Krasrepen/DISTRIBUTORE-AUTOMATICO/schema elettrico/SchemaElettrico.kicad_sch

## KiCad design schema elettrico/SchemaElettrico.kicad_sch (2025-07-13)

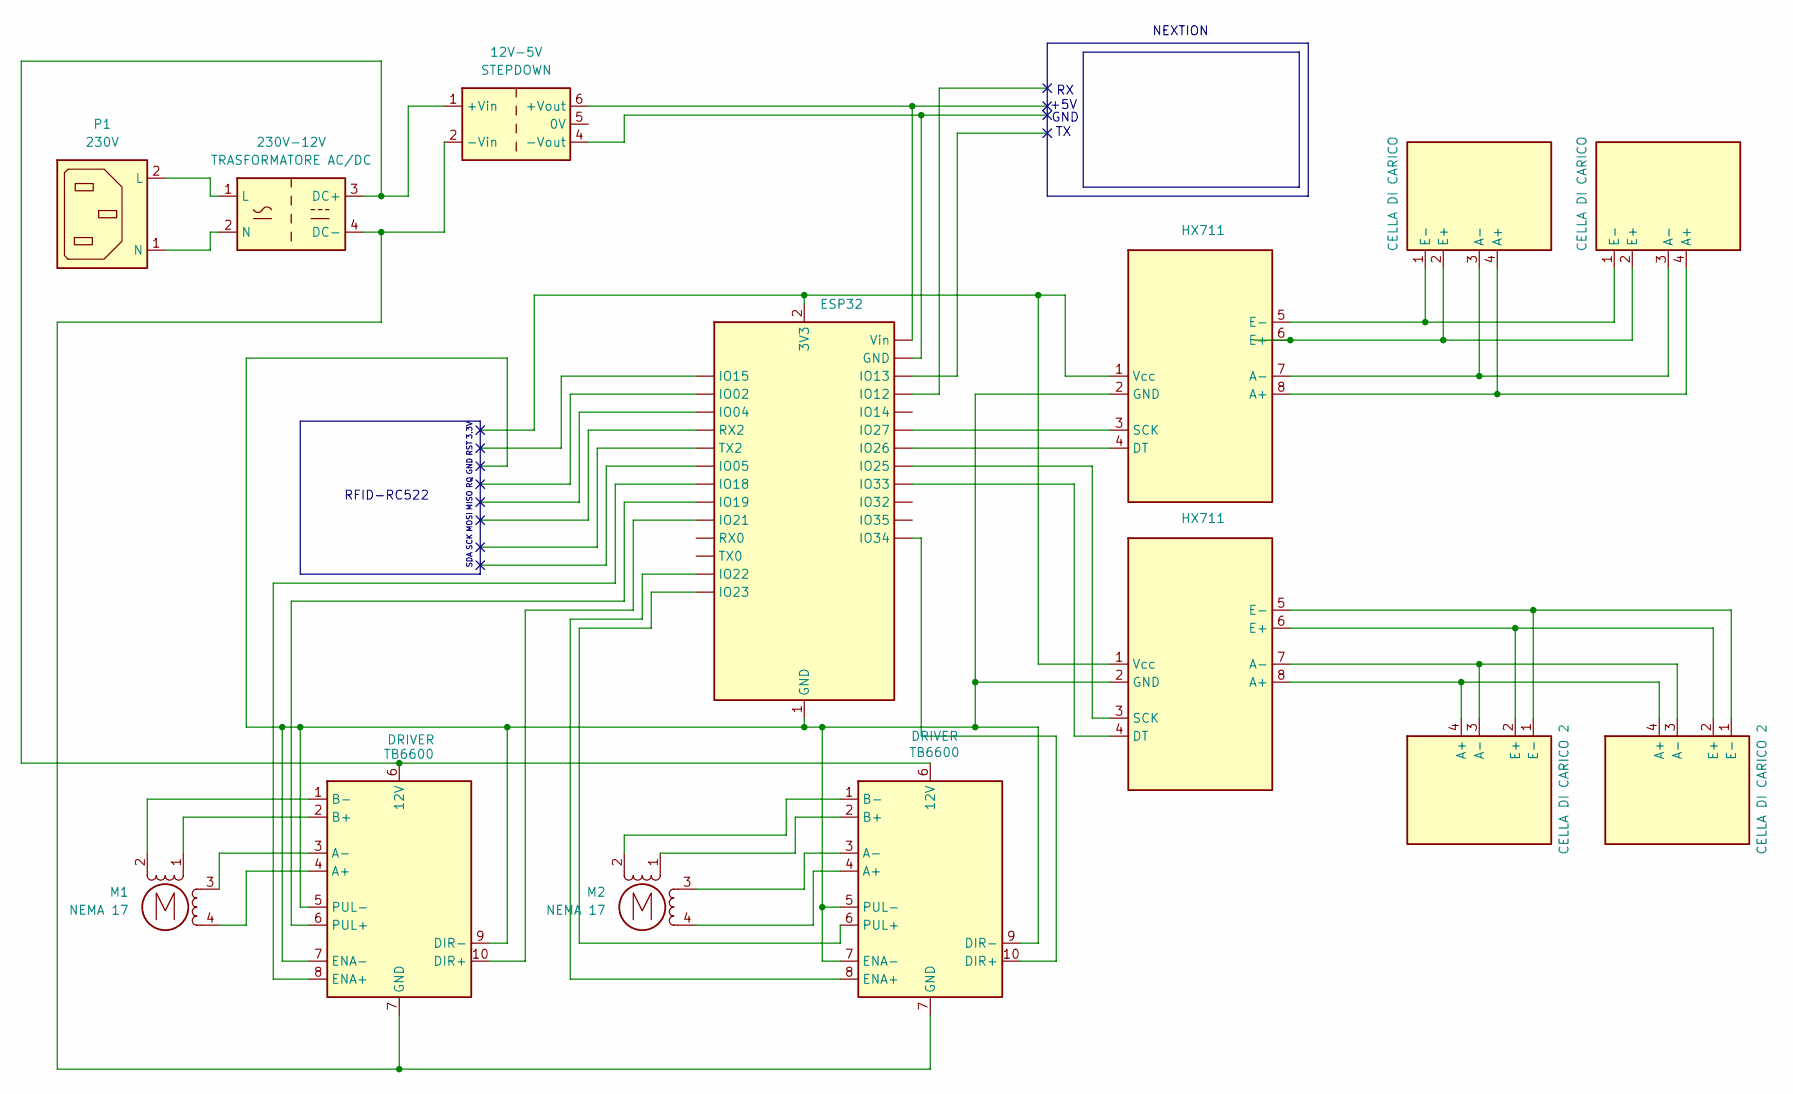
[picture p2: schematic SchemaElettrico.kicad_sch]

Parts:
12V-5V: STEPDOWN; Converter_DCDC_XP_POWER-IAxxxxS_THT
230V-12V: TRASFORMATORE AC/DC; Converter_ACDC_Vigortronix_VTX-214-010-1xx_THT
DRIVER: TB6600; VQFN-16-1EP_3x3mm_P0.5mm_EP1.8x1.8mm
M1, M2: NEMA 17
P1: 230V
U1: ESP32; ESP32-S2-WROVER
U2, U3: HX711; SOP-16_3.9x9.9mm_P1.27mm
U4, U6: CELLA DI CARICO; SOIC-8_3.9x4.9mm_P1.27mm
U5, U7: CELLA DI CARICO 2; SOIC-8_3.9x4.9mm_P1.27mm

Connections:
unnamed: 12V-5V.1 (+Vin), 230V-12V.3 (DC+), DRIVER.6 (PUL+)
unnamed: 12V-5V.2 (-Vin), 230V-12V.4 (DC-), DRIVER.7 (ENA-), DRIVER.17 (GND)
unnamed: 12V-5V.4 (-Vout), U1. (IO15)
unnamed: 12V-5V.6 (+Vout), U1. (IO15)
unnamed: 230V-12V.1 (L), P1.2 (L)
unnamed: 230V-12V.2 (N), P1.1 (N)
unnamed: DRIVER.1 (B-), M1.2 (-), M2.2 (-)
unnamed: DRIVER.2 (B+), M1.1, M2.1
unnamed: DRIVER.3 (A-), M1.3, M2.3
unnamed: DRIVER.4 (A+), M1.4, M2.4
unnamed: DRIVER.5 (PUL-), DRIVER.7 (ENA-), DRIVER.9 (DIR-), U1.1 (GND), U1.26 (GND), U1.42 (GND), U1.43 (GND), U2.2 (BASE), U3.2 (BASE)
unnamed: DRIVER.6 (PUL+), U1. (IO15)
unnamed: DRIVER.8 (ENA+), U1. (IO15)
unnamed: DRIVER.10 (OUTW), U1. (IO15)
unnamed: U1.2 (3V3), U2.1 (Vcc), U3.1 (Vcc)
unnamed: U1. (IO15), U2.3 (AVDD), U2.4 (VFB), U3.3 (AVDD), U3.4 (VFB)
unnamed: U2.5 (AGND), U4.1 (E-), U6.1 (E-)
unnamed: U2.6 (VBG), U4.2 (E+), U6.2 (E+)
unnamed: U2.7 (A-), U4.3 (A-), U6.3 (A-)
unnamed: U2.8 (A+), U4.4 (A+), U6.4 (A+)
unnamed: U3.5 (AGND), U5.1 (E-), U7.1 (E-)
unnamed: U3.6 (VBG), U5.2 (E+), U7.2 (E+)
unnamed: U3.7 (A-), U5.3 (A-), U7.3 (A-)
unnamed: U3.8 (A+), U5.4 (A+), U7.4 (A+)

Notes on the sheet:
GND
3.3V
RST
SCK
SDA
MOSI
+5V
RFID-RC522
MISO
NEXTION
